dimaib/UART_Key/uart_key/uart_key-F_Cu.dxf

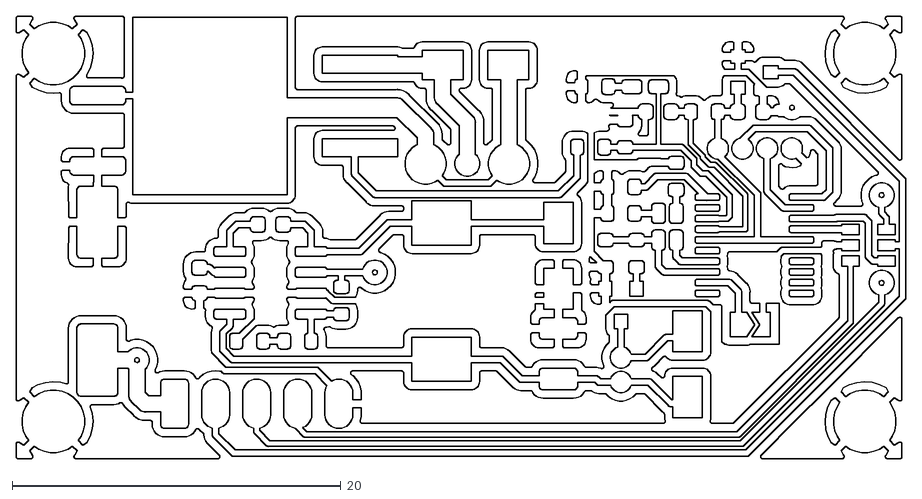
[picture p7: CAD file, 2022-04-17]
uart_key/uart_key-F_Cu.dxf
54.2 x 26.9
