dimaib/UART_Key/box_develop/Magnet_conn.SLDPRT

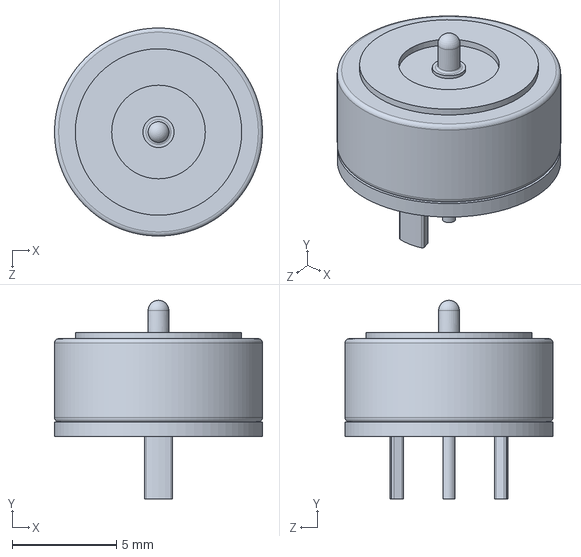
[picture p8: CAD file, 2022-04-17]
box_develop/Magnet_conn.SLDPRT
10.0 x 9.55 x 10.0 mm
