dimaib/UART_Key/box_develop/magnit.SLDPRT

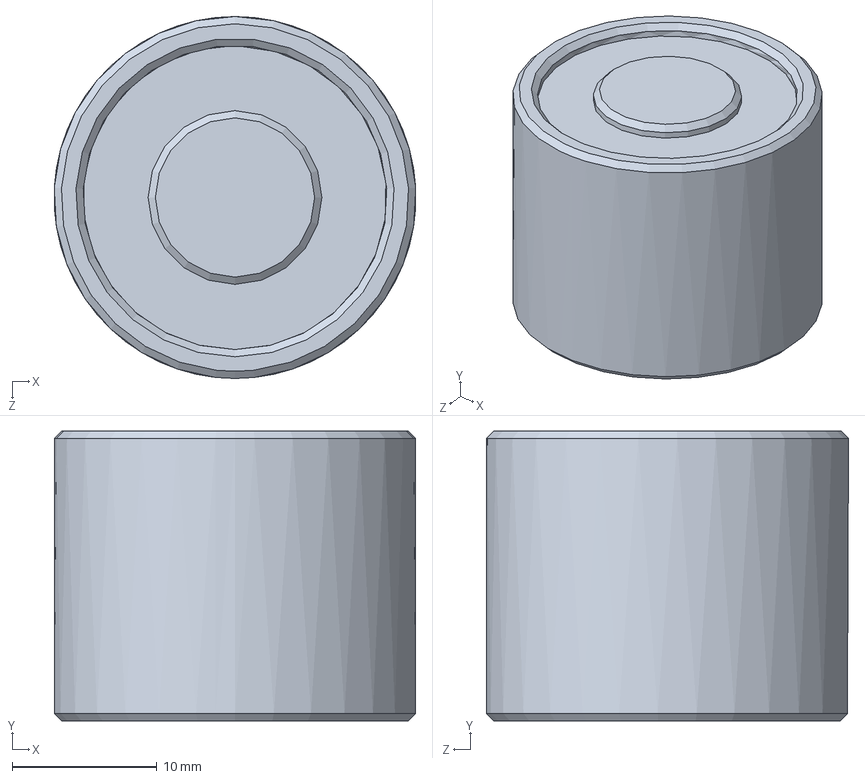
[picture p9: CAD file, 2022-04-17]
box_develop/magnit.SLDPRT
25.0 x 20.0 x 25.0 mm
