dimaib/UART_Key/box_develop/ZH_04x01_1.5mm.SLDPRT

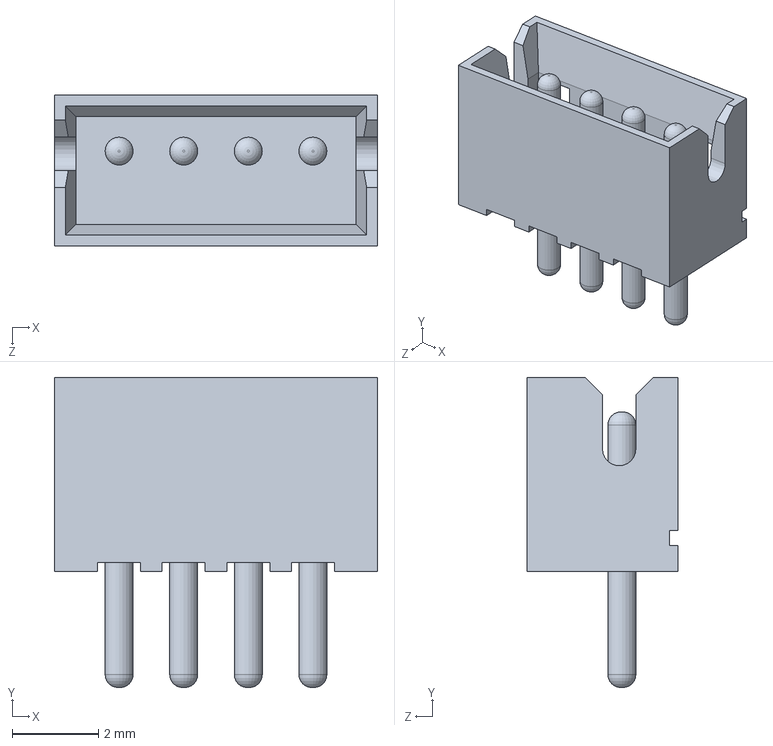
[picture p10: CAD file, 2022-04-17]
box_develop/ZH_04x01_1.5mm.SLDPRT
7.50 x 7.20 x 3.50 mm
