dimaib/UART_Key/box_develop/in_os.SLDPRT

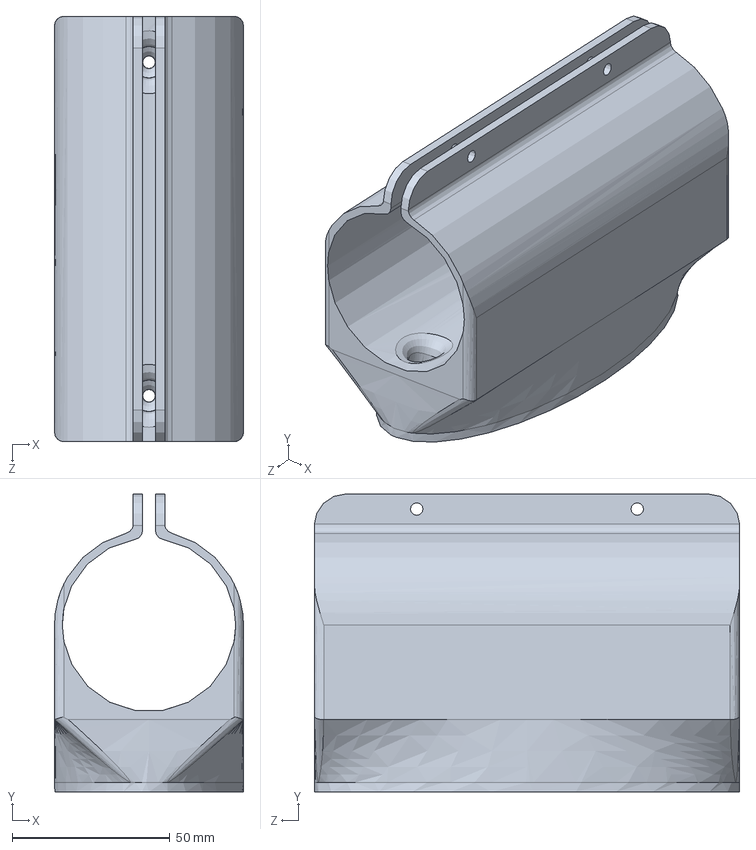
[picture p11: CAD file, 2022-04-17]
box_develop/in_os.SLDPRT
60.0 x 94.6 x 135.0 mm
