dimaib/UART_Key/box_develop/ZH_02x01_1.5mm.SLDPRT

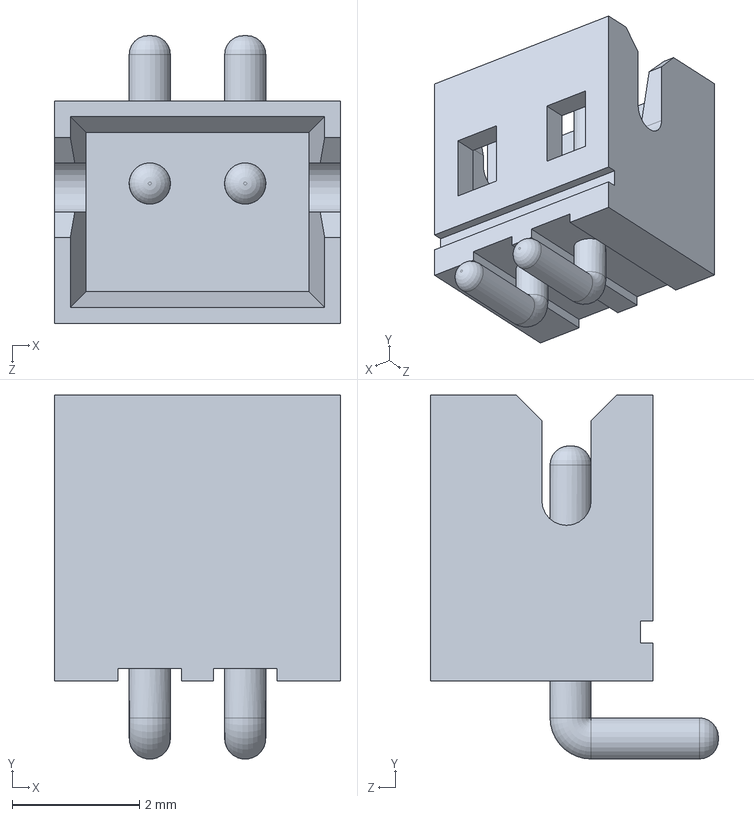
[picture p12: CAD file, 2022-04-17]
box_develop/ZH_02x01_1.5mm.SLDPRT
4.50 x 5.72 x 4.53 mm
